AllWize/AllWizeK1-hardware/RevA/Bot.png

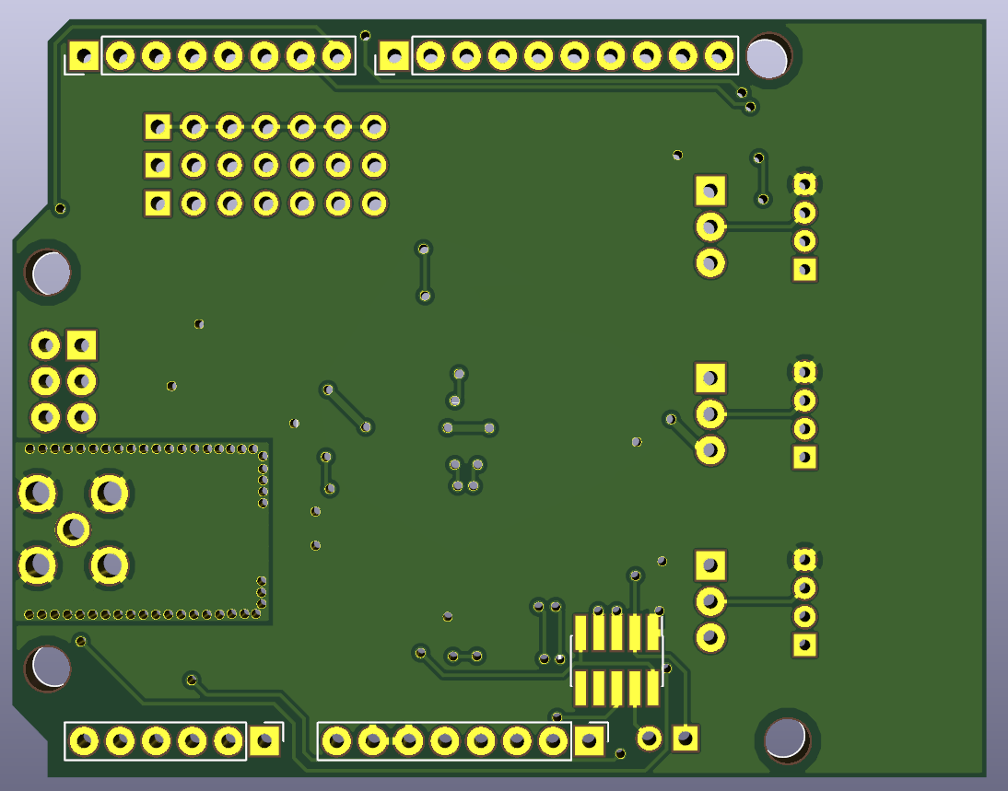
RevA/Bot.png
