AllWize/AllWizeK1-hardware/RevA/osh.png

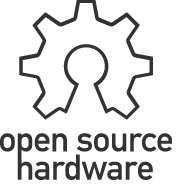
RevA/osh.png
