AllWize/AllWizeK1-hardware/RevA/Top.png

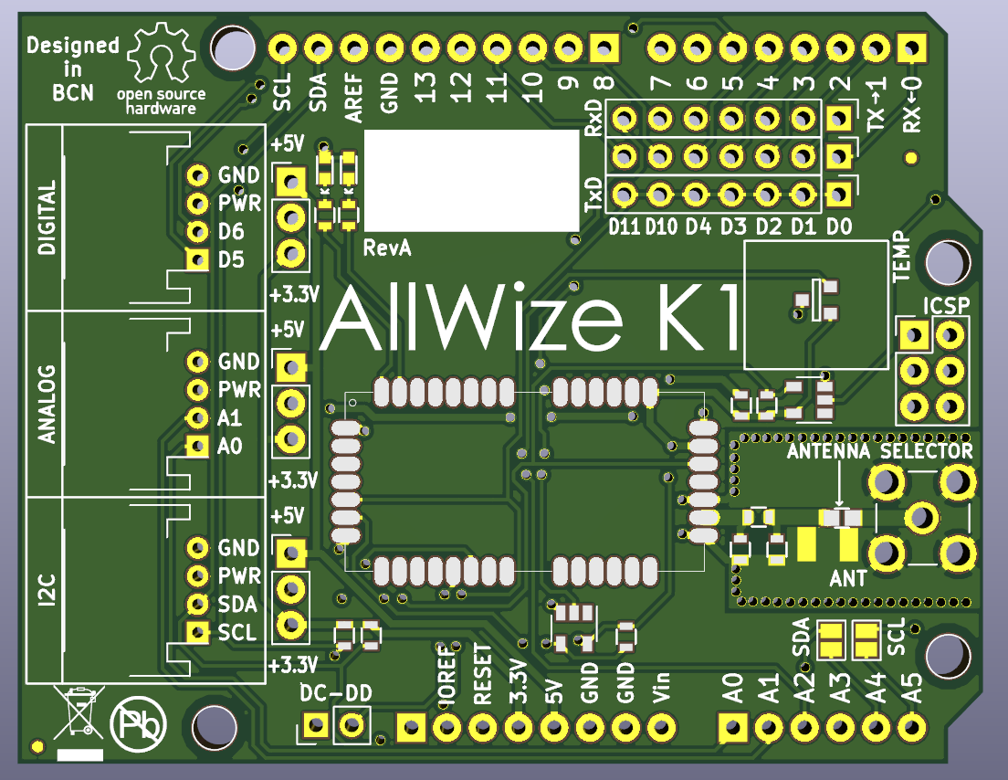
RevA/Top.png
