AllWize/AllWizeK1-hardware/RevPA/pcb/PCB-view-2-TOP.png

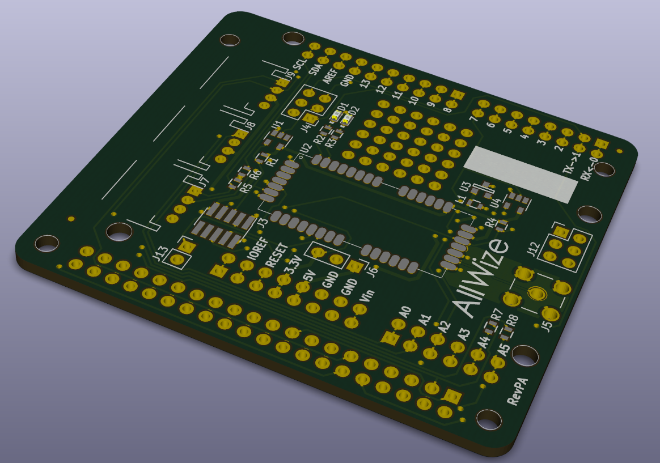
RevPA/pcb/PCB-view-2-TOP.png
